techyg/Voron0Stuff/SiboorV02kit/PrinterConfigs/gcodemacros.cfg

## To be used with BED_SCREWS_ADJUST
[bed_screws]
screw1: 60,5
screw1_name: front screw
screw2: 10,110
screw2_name: back left
screw3: 110,110
screw3_name: back right

[gcode_macro LEVEL_BED]
gcode:
    G28
    BED_SCREWS_ADJUST


#####################################################################
# Macros
#####################################################################

[gcode_macro DISABLE_STEPPERS]
#Disables Steppers
gcode:
    M84

[gcode_macro PRINT_START]
#   Use PRINT_START for the slicer starting script - please customize for your slicer of choice
gcode:
    G28                            ; home all axes
    G90                            ; absolute positioning    
    G1 Z20 F3000                   ; move nozzle away from bed
   
[gcode_macro PRINT_END]
#   Use PRINT_END for the slicer ending script - please customize for your slicer of choice
gcode:
    M400                           ; wait for buffer to clear
    G92 E0                         ; zero the extruder
    G1 E-4.0 F3600                 ; retract filament
    G91                            ; relative positioning

    #   Get Boundaries
    {% set max_x = printer.configfile.config["stepper_x"]["position_max"]|float %}
    {% set max_y = printer.configfile.config["stepper_y"]["position_max"]|float %}
    {% set max_z = printer.configfile.config["stepper_z"]["position_max"]|float %}

    #   Check end position to determine safe direction to move
    {% if printer.toolhead.position.x < (max_x - 20) %}
        {% set x_safe = 20.0 %}
    {% else %}
        {% set x_safe = -20.0 %}
    {% endif %}

    {% if printer.toolhead.position.y < (max_y - 20) %}
        {% set y_safe = 20.0 %}
    {% else %}
        {% set y_safe = -20.0 %}
    {% endif %}

    {% if printer.toolhead.position.z < (max_z - 2) %}
        {% set z_safe = 2.0 %}
    {% else %}
        {% set z_safe = max_z - printer.toolhead.position.z %}
    {% endif %}

    G0 Z{z_safe} F3600             ; move nozzle up
    G0 X{x_safe} Y{y_safe} F20000  ; move nozzle to remove stringing
    TURN_OFF_HEATERS
    M107                           ; turn off fan
    G90                            ; absolute positioning
    G0 X60 Y{max_y} F3600          ; park nozzle at rear
  
[gcode_macro LOAD_FILAMENT]
gcode:
   M83                            ; set extruder to relative
   G1 E30 F300                    ; load
   G1 E15 F150                    ; prime nozzle with filament
   M82                            ; set extruder to absolute
    
[gcode_macro UNLOAD_FILAMENT]
gcode:
   M83                            ; set extruder to relative
   G1 E10 F300                    ; extrude a little to soften tip
   G1 E-40 F1800                  ; retract some, but not too much or it will jam
   M82                            ; set extruder to absolute


#### Macros copied from Siboor ###################################################

[gcode_macro SHUTDOWN]
gcode:
  {action_call_remote_method("shutdown_machine")}
[pause_resume]

[display_status]

################################################################################
################################################################################


[gcode_macro CANCEL_PRINT]
rename_existing: BASE_CANCEL_PRINT
gcode:
    TURN_OFF_HEATERS
    CLEAR_PAUSE
    G91 
    G1 Z5 
    G90
    G92 E0
    G1 X118 Y118 E-3
    G92 E0
    M84 XYE
    SDCARD_RESET_FILE
    BASE_CANCEL_PRINT

[gcode_macro RESUME]
rename_existing: BASE_RESUME
#default_parameter_E: 1      # edit to your preferred retract length
gcode:
    G91
    G1 E{E} F2100
    G90
    RESTORE_GCODE_STATE NAME=PAUSE_state MOVE=1
    BASE_RESUME

[gcode_macro PAUSE]
rename_existing: BASE_PAUSE
gcode:
    SAVE_GCODE_STATE NAME=PAUSE_state
    BASE_PAUSE
    G91
    G1 E-{E} F2100
    G1 Z{Z}
    G90
    G1 X{X} Y{Y} F6000
