techyg/Voron0Stuff/SiboorV02kit/PrinterConfigs/sensorless.cfg

##Taken from here: https://github.com/EricZimmerman/Voron02/blob/master/macros/helpers/homing.cfg

#required for SET_KINEMATIC_POSITION to work.

[force_move]
enable_force_move: true

[gcode_macro _HOME_X]
gcode:
    # Home
    {% set RUN_CURRENT_X = printer.configfile.settings['tmc2209 stepper_x'].run_current|float %}
    {% set RUN_CURRENT_Y = printer.configfile.settings['tmc2209 stepper_y'].run_current|float %}
    {% set HOME_CURRENT = 1.1 %}
    SET_TMC_CURRENT STEPPER=stepper_x CURRENT={HOME_CURRENT}
    SET_TMC_CURRENT STEPPER=stepper_y CURRENT={HOME_CURRENT}
    
    SET_KINEMATIC_POSITION X=15
    G91
    G1 X-10 F1200
    
    G4 P2000
    G28 X
    
    # Move away
    G91
    G1 X-10 F1200
    
    SET_TMC_CURRENT STEPPER=stepper_x CURRENT={RUN_CURRENT_X}
    SET_TMC_CURRENT STEPPER=stepper_y CURRENT={RUN_CURRENT_Y}

[gcode_macro _HOME_Y]
gcode:
    {% set RUN_CURRENT_X = printer.configfile.settings['tmc2209 stepper_x'].run_current|float %}
    {% set RUN_CURRENT_Y = printer.configfile.settings['tmc2209 stepper_y'].run_current|float %}
    {% set HOME_CURRENT = 1.1 %}
    SET_TMC_CURRENT STEPPER=stepper_x CURRENT={HOME_CURRENT}
    SET_TMC_CURRENT STEPPER=stepper_y CURRENT={HOME_CURRENT}
    
    SET_KINEMATIC_POSITION Y=15
    G91
    G1 Y-10 F1200
    G4 P2000
    # Home
    G28 Y
    # Move away
    G91
    G1 Y-10 F1200

    # Wait just a second… (give StallGuard registers time to clear)
    SET_TMC_CURRENT STEPPER=stepper_x CURRENT={RUN_CURRENT_X}
    SET_TMC_CURRENT STEPPER=stepper_y CURRENT={RUN_CURRENT_Y}


[homing_override]
axes: xyz
gcode:
  {% set home_all = 'X' not in params and 'Y' not in params and 'Z' not in params %}

  SET_KINEMATIC_POSITION Z=1
  G1 Z4 F1200

  {% if home_all or 'X' in params %}
    _HOME_X
  {% endif %}
  
  {% if home_all or 'Y' in params %}
    _HOME_Y
  {% endif %}
  
  {% if home_all or 'Z' in params %}
  
    G28 Z
    G90
    G1 Z60 F1500
  {% endif %}
