techyg/Voron0Stuff/SiboorV02kit/PrinterConfigs/DisplayEncoder.cfg

[mcu display]
serial: /dev/serial/by-id/usb-Klipper_stm32f042x6_JKYZ-if00
restart_method: command

[display]
lcd_type: sh1106
i2c_mcu: display
i2c_bus: i2c1a
encoder_pins: ^display:PA4, ^display:PA3
click_pin: ^!display:PA1
kill_pin: ^!display:PA5
x_offset: 2

[neopixel displayStatus]
pin: display:PA0
chain_count: 1
color_order: GRB
initial_RED: 0.2
initial_GREEN: 0.05
initial_BLUE: 0
